juangallego89/caudalimetro/Documentación/imagenes/bd.jpg

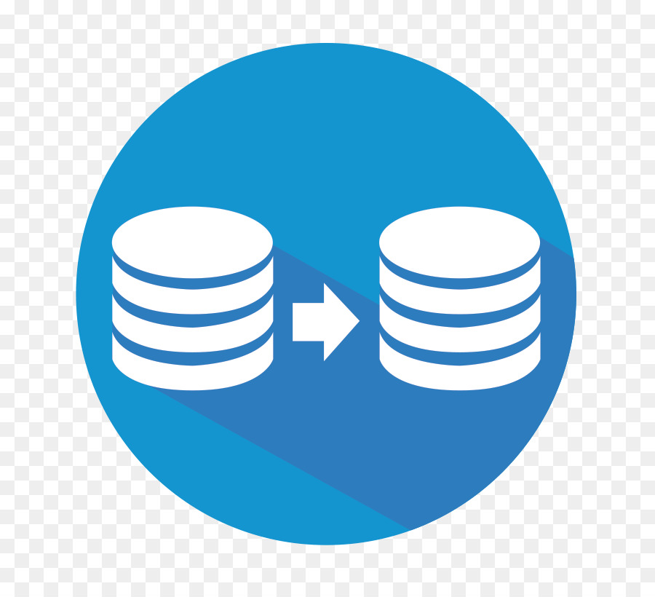
Documentación/imagenes/bd.jpg
