juangallego89/caudalimetro/Documentación/imagenes/CIRCUITO.png

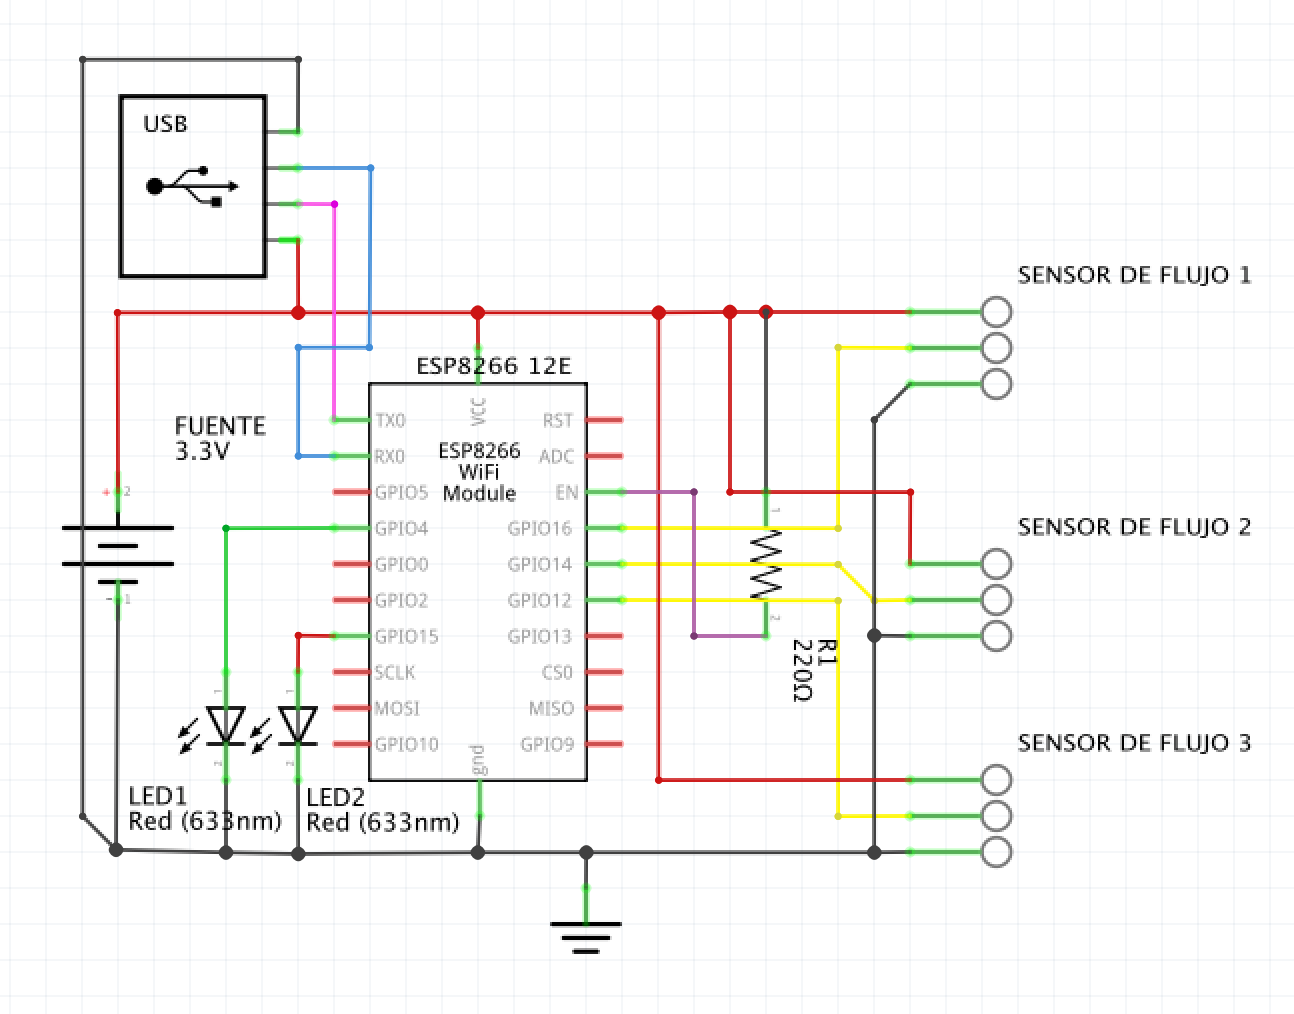
Documentación/imagenes/CIRCUITO.png
