juangallego89/caudalimetro/Documentación/imagenes/CIRCUITO_1.png

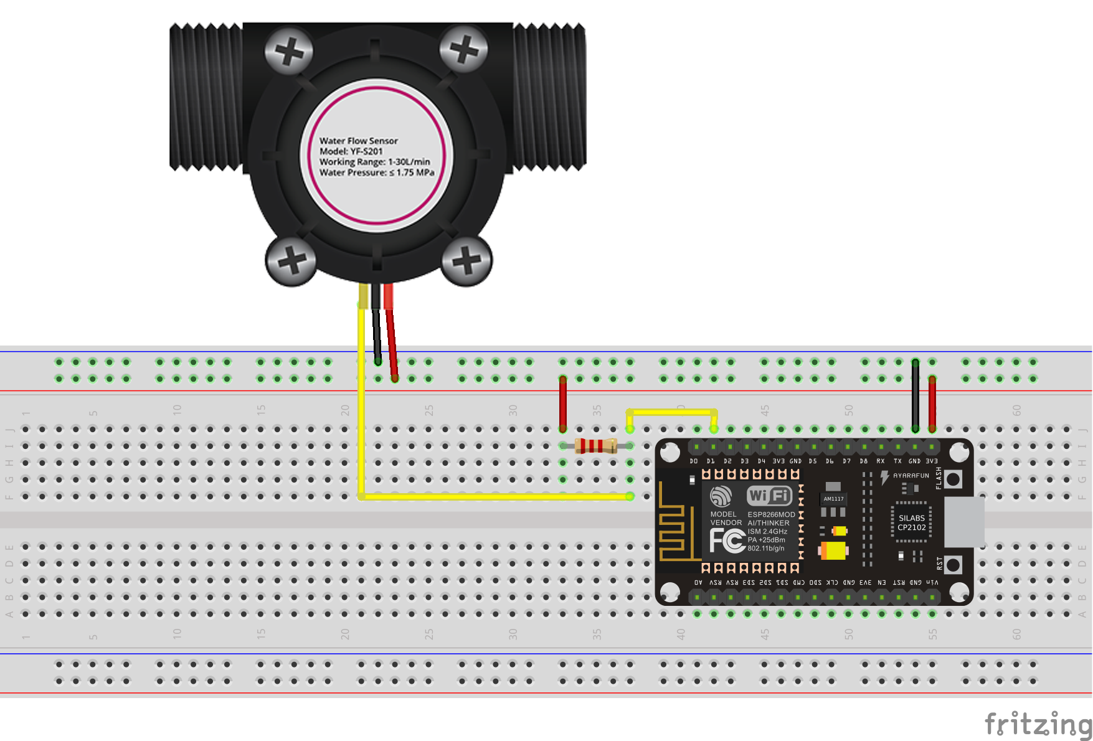
Documentación/imagenes/CIRCUITO_1.png
