juangallego89/caudalimetro/Documentación/imagenes/FIRMWARE ESP12E.png

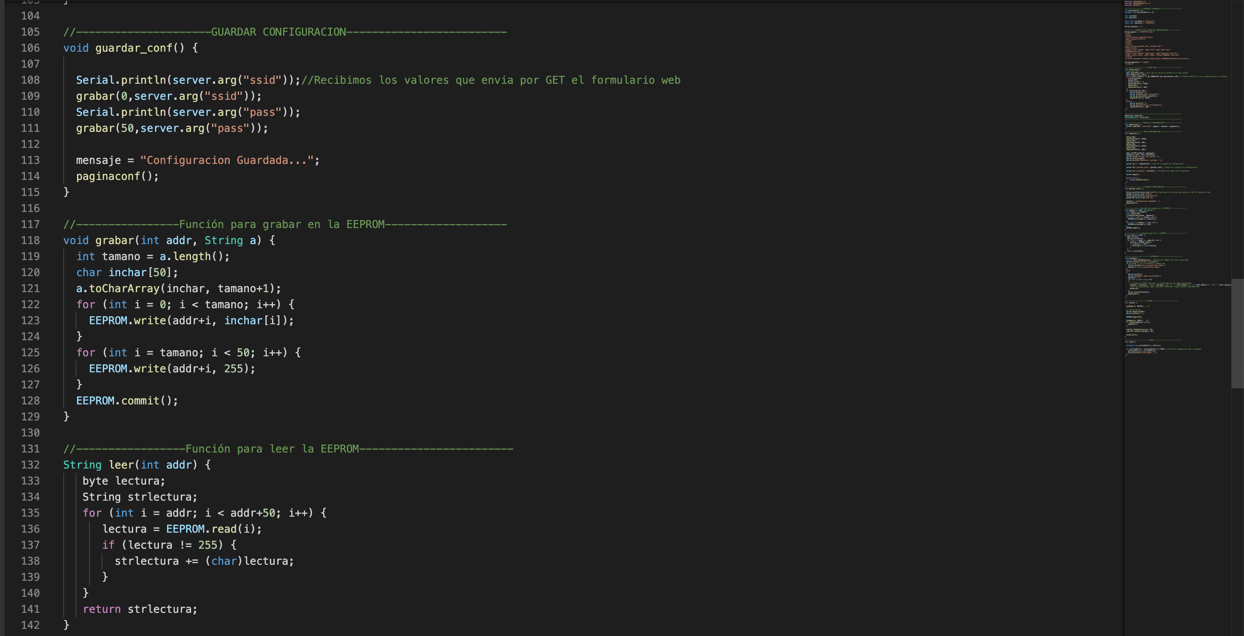
Documentación/imagenes/FIRMWARE ESP12E.png
