juangallego89/caudalimetro/Documentación/imagenes/IOT3.png

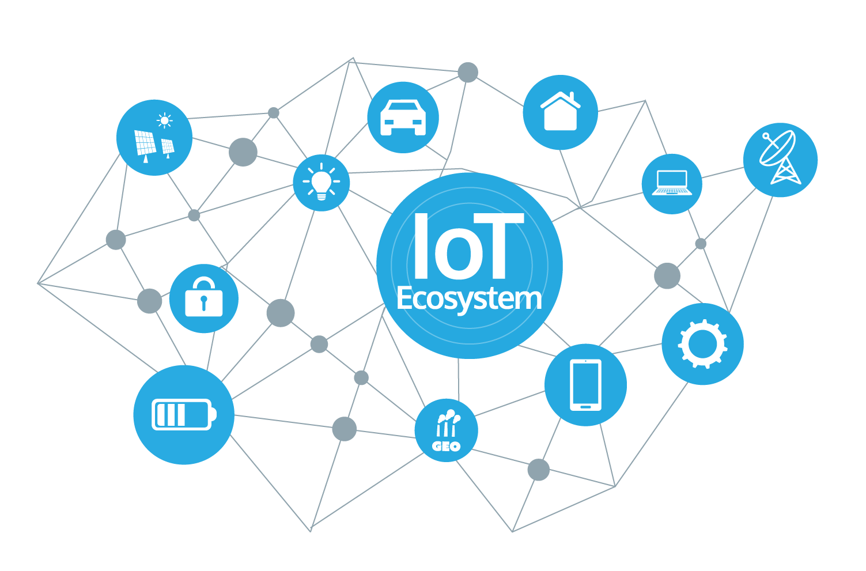
Documentación/imagenes/IOT3.png
