juangallego89/caudalimetro/Documentación/imagenes/iot.png

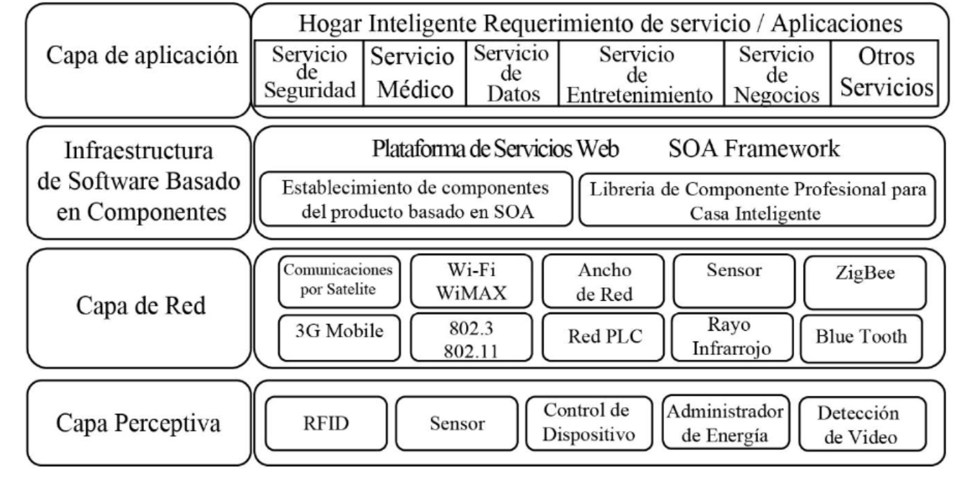
Documentación/imagenes/iot.png
