juangallego89/caudalimetro/Documentación/imagenes/MER.png

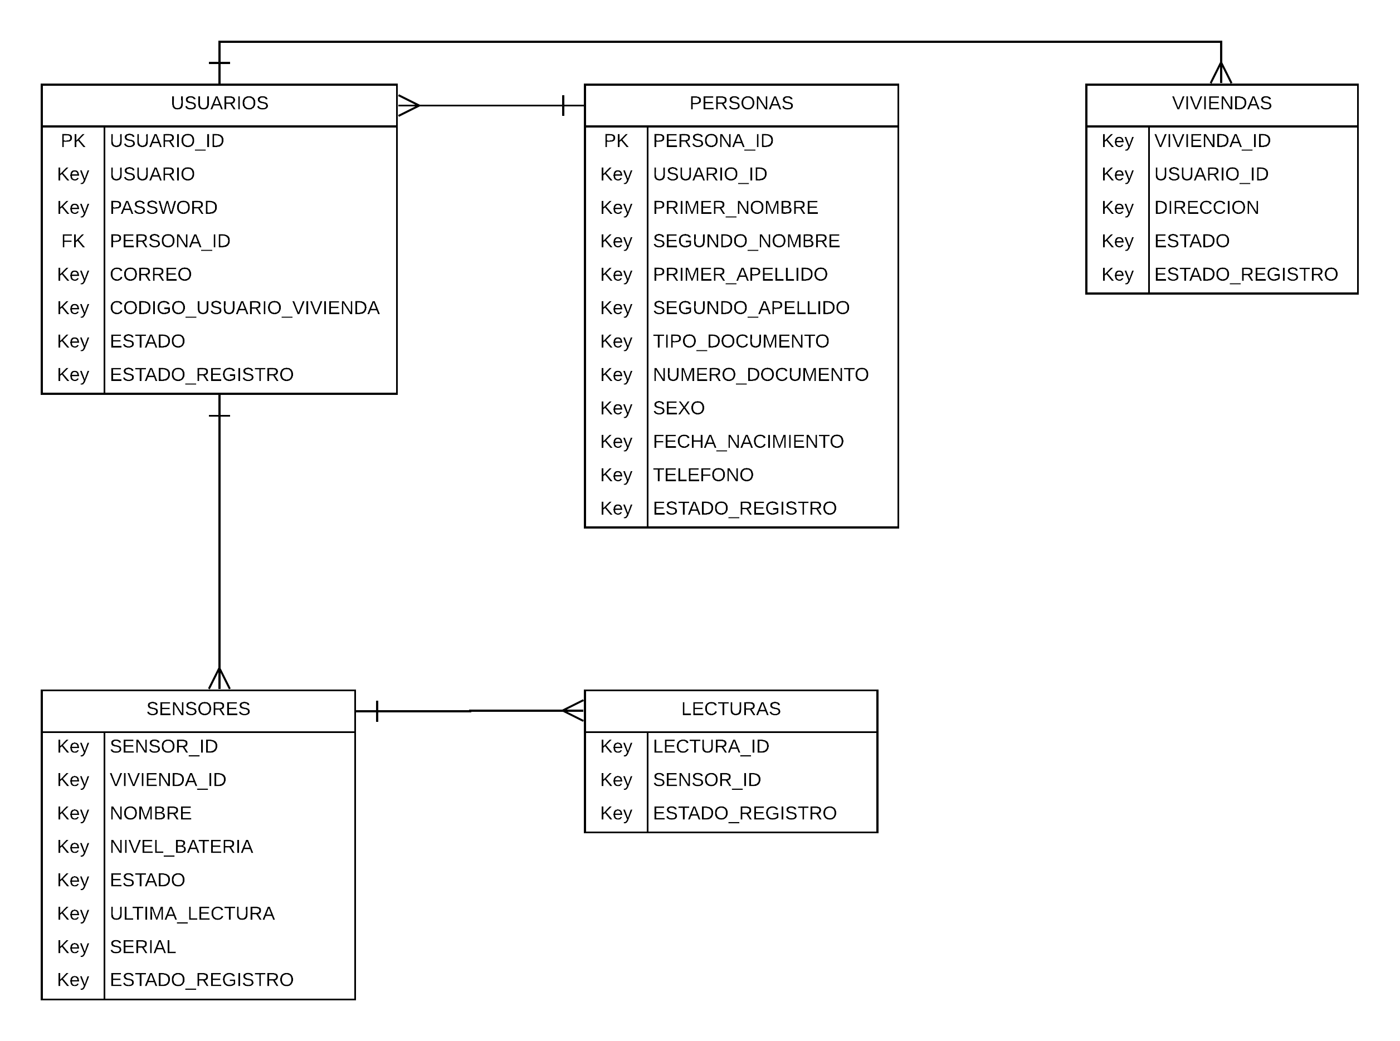
Documentación/imagenes/MER.png
