juangallego89/caudalimetro/Documentación/imagenes/ScriptBD.png

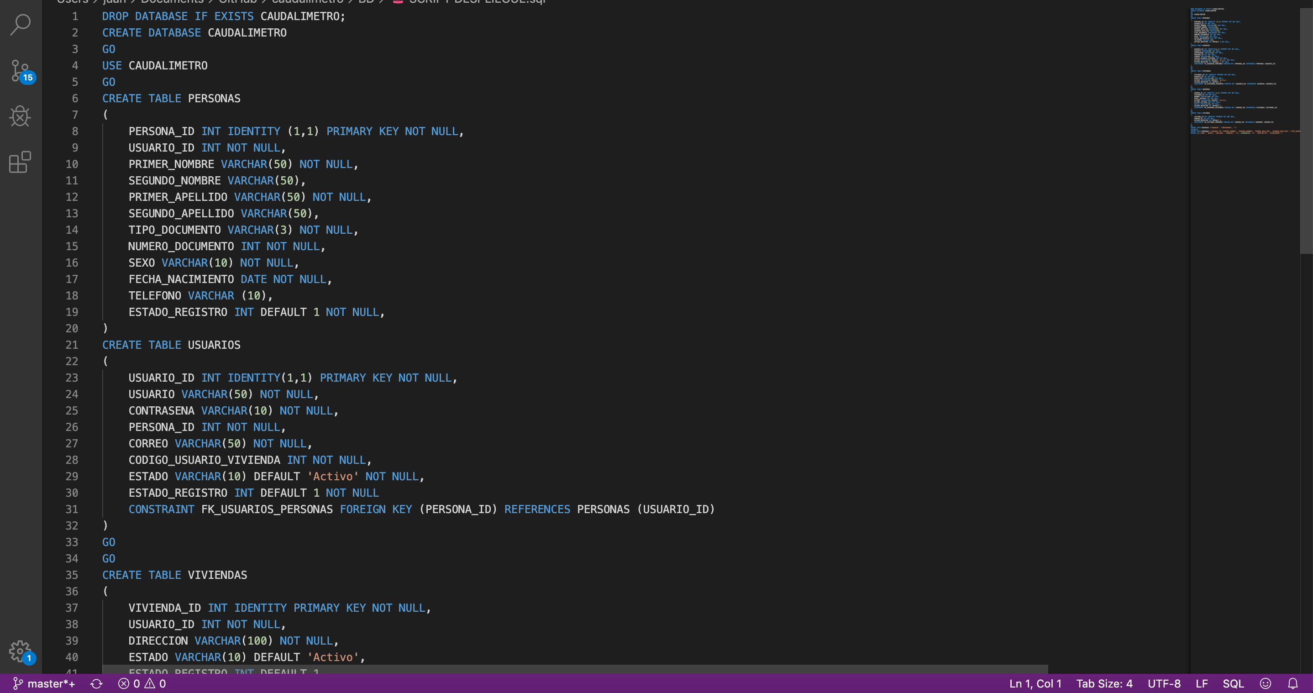
Documentación/imagenes/ScriptBD.png
