juangallego89/caudalimetro/Documentación/imagenes/web-services.png

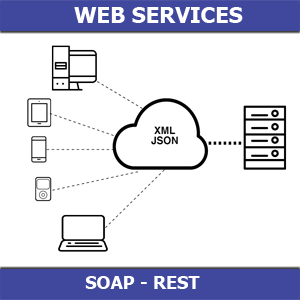
Documentación/imagenes/web-services.png
