juangallego89/caudalimetro/Hardware/Prototipos/IMG_20200115_150700.jpg

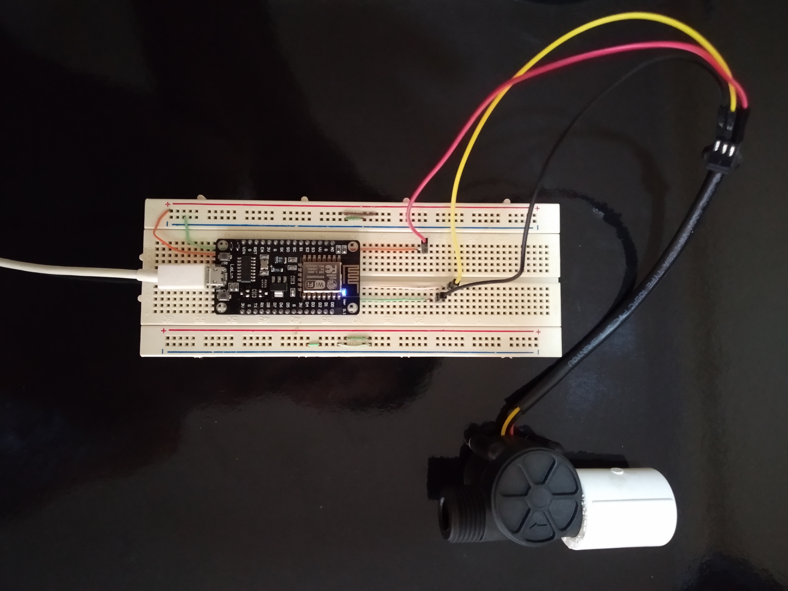
Hardware/Prototipos/IMG_20200115_150700.jpg
