juangallego89/caudalimetro/Hardware/Prototipos/IMG_20200115_151654.jpg

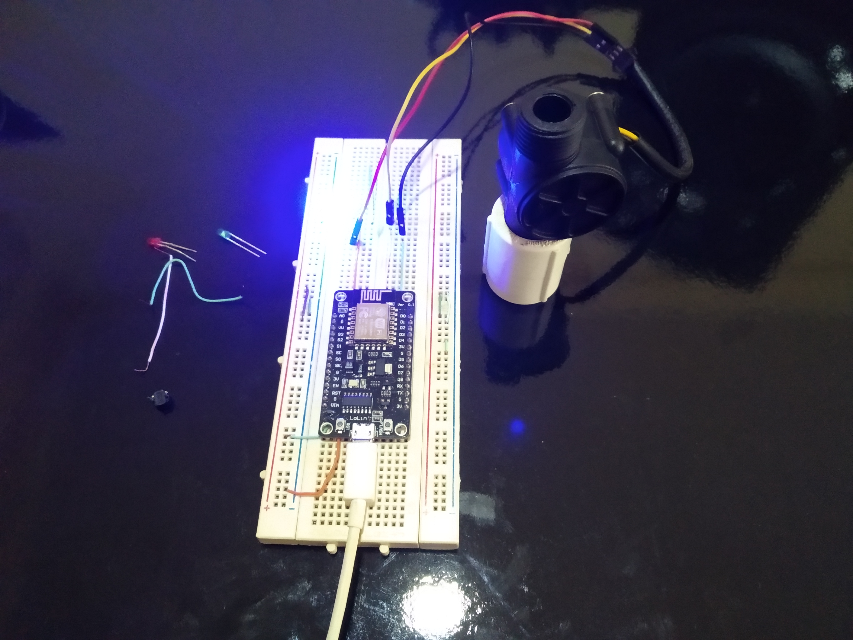
Hardware/Prototipos/IMG_20200115_151654.jpg
