juangallego89/caudalimetro/Hardware/Prototipos/IMG_20200115_151741.jpg

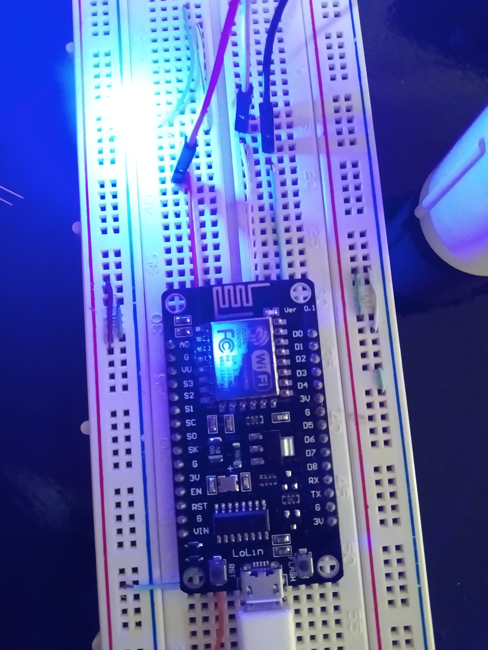
Hardware/Prototipos/IMG_20200115_151741.jpg
